1-rafael-1/pi-pico-alarmclock-rust/src/task/sound.rs

//! # Sound task
//!  This module contains the task that plays sound using the `DFPlayer` Mini module.
//!
//! The task is responsible for initializing the `DFPlayer` Mini module, powering it on, playing a sound, and powering it off.
use core::sync::atomic::{AtomicBool, Ordering};

use defmt::{Debug2Format, info};
use dfplayer_async::{DfPlayer, Equalizer, PlayBackSource, TimeSource};
use embassy_futures::select::{Either, select};
use embassy_rp::{
    gpio::{Input, Output},
    uart::BufferedUart,
};
use embassy_sync::{blocking_mutex::raw::CriticalSectionRawMutex, mutex::Mutex, signal::Signal};
use embassy_time::{Delay, Duration, Instant, Timer};

use crate::event::{Event, send_event};

/// Signal for starting the sound
static SOUND_START_SIGNAL: Signal<CriticalSectionRawMutex, ()> = Signal::new();

/// Signal for stopping the sound
static SOUND_STOP_SIGNAL: Signal<CriticalSectionRawMutex, ()> = Signal::new();

/// Tracks whether the `DFPlayer` is currently powered on
static DFPLAYER_POWERED: AtomicBool = AtomicBool::new(false);

/// Current volume level (protected by mutex)
static SOUND_VOLUME: Mutex<CriticalSectionRawMutex, u8> = Mutex::new(13);

/// Updates the current volume level
pub fn signal_sound_volume_update(volume: u8) {
    // We need to update the volume in the mutex
    // This will be picked up next time sound plays
    // Use try_lock to avoid blocking
    if let Ok(mut vol) = SOUND_VOLUME.try_lock() {
        *vol = volume;
    } else {
        info!("Volume update skipped: mutex locked");
    }
}

/// Gets the current volume level
async fn get_current_volume() -> u8 {
    let vol = SOUND_VOLUME.lock().await;
    *vol
}

/// Signals the sound task to start playing
pub fn signal_sound_start() {
    SOUND_START_SIGNAL.signal(());
}

/// Signals the sound task to stop playing
/// Only signals if the `DFPlayer` is currently powered to avoid pending signals
pub fn signal_sound_stop() {
    // Only signal stop if DFPlayer is actually powered and potentially playing
    if DFPLAYER_POWERED.load(Ordering::Relaxed) {
        SOUND_STOP_SIGNAL.signal(());
    } else {
        info!("Skipping sound stop signal - DFPlayer not powered");
    }
}

/// Waits for the next sound start signal
async fn wait_for_sound_start() {
    SOUND_START_SIGNAL.wait().await;
}

/// Waits for the next sound stop signal
async fn wait_for_sound_stop() {
    SOUND_STOP_SIGNAL.wait().await;
}

// Time source implementation for DFPlayer
/// Time source implementation for the `DFPlayer` using Embassy's `Instant`.
struct MyTimeSource;

impl TimeSource for MyTimeSource {
    type Instant = Instant;

    fn now(&self) -> Self::Instant {
        Instant::now()
    }

    fn is_elapsed(&self, since: Self::Instant, timeout_ms: u64) -> bool {
        Instant::now().duration_since(since) >= Duration::from_millis(timeout_ms)
    }
}

/// Waits for the busy pin to go high (indicating playback finished)
/// The busy pin is LOW during playback and HIGH when idle/finished
async fn wait_for_music_end(busy_pin: &mut Input<'static>) {
    // Wait for the pin to go high (song finished)
    // We add a small initial delay to ensure the pin has stabilized after starting playback
    Timer::after(Duration::from_millis(100)).await;
    busy_pin.wait_for_high().await;
}

/// Powers on the `DFPlayer` module and waits for it to stabilize
async fn power_on_dfplayer(pwr: &mut Output<'static>) {
    info!("Powering on the dfplayer");
    pwr.set_high();
    DFPLAYER_POWERED.store(true, Ordering::Relaxed);
    Timer::after(Duration::from_millis(500)).await;
    info!("Powered on the dfplayer");
}

/// Powers off the `DFPlayer` module
fn power_off_dfplayer(pwr: &mut Output<'static>) {
    info!("Powering off the dfplayer");
    pwr.set_low();
    DFPLAYER_POWERED.store(false, Ordering::Relaxed);
}

/// Handles the sound playback after `DFPlayer` initialization
async fn handle_playback(dfp: &mut DfPlayer<'_, BufferedUart, MyTimeSource, Delay>, busy_pin: &mut Input<'static>) {
    info!("Playing sound");

    // Step 1: Configure volume
    let volume = get_current_volume().await;
    info!("Setting volume to {}", volume);
    let _ = dfp.set_volume(volume).await;
    Timer::after(Duration::from_millis(100)).await;

    // Step 2: Set equalizer
    let _ = dfp.set_equalizer(Equalizer::Classic).await;
    Timer::after(Duration::from_millis(100)).await;

    // Step 3: Set playback source
    let _ = dfp.set_playback_source(PlayBackSource::SDCard).await;
    Timer::after(Duration::from_millis(100)).await;

    // Step 4: Start playback
    let _ = dfp.play(1).await;
    Timer::after(Duration::from_millis(200)).await;

    // Step 5: Wait for playback to complete
    wait_for_playback_end(busy_pin).await;
}

/// Waits for playback to end either by user action or song completion
async fn wait_for_playback_end(busy_pin: &mut Input<'static>) {
    let result = select(wait_for_sound_stop(), wait_for_music_end(busy_pin)).await;

    match result {
        Either::First(()) => {
            info!("Sound stopped by user");
        }
        Either::Second(()) => {
            info!("Sound finished playing (busy pin high)");
            // Notify that the alarm should stop since the song ended
            send_event(Event::AlarmStop).await;
        }
    }
}

/// Initializes the `DFPlayer` and handles playback if successful
async fn initialize_and_play(uart: &mut BufferedUart, busy_pin: &mut Input<'static>) {
    // Initialize DFPlayer
    let feedback_enable = false;
    let timeout = Duration::from_secs(1);
    let reset_duration_override = Some(Duration::from_millis(1000));

    let time_source = MyTimeSource;
    let delay = Delay;

    let dfp_result = DfPlayer::new(
        uart,
        feedback_enable,
        timeout.as_millis(),
        time_source,
        delay,
        reset_duration_override.map(|d| d.as_millis()),
    )
    .await;

    // Handle the result
    match dfp_result {
        Ok(mut dfp) => {
            info!("DfPlayer initialized successfully");
            handle_playback(&mut dfp, busy_pin).await;
        }
        Err(ref e) => {
            info!("DfPlayer initialization failed with error {:?}", Debug2Format(&e));
        }
    }
}

#[embassy_executor::task]
pub async fn sound_handler(mut uart: BufferedUart, mut pwr: Output<'static>, mut busy_pin: Input<'static>) {
    info!("Sound task started");

    loop {
        // Wait for start signal
        wait_for_sound_start().await;

        // Power on DFPlayer
        power_on_dfplayer(&mut pwr).await;

        // Initialize and play sound
        initialize_and_play(&mut uart, &mut busy_pin).await;

        // Power off DFPlayer
        power_off_dfplayer(&mut pwr);
    }
}
