1-rafael-1/pi-pico-alarmclock-rust/src/task/mod.rs

//! Tasks that make up the application.
pub mod alarm_settings;
pub mod alarm_trigger;
pub mod button_leds;
pub mod buttons;
pub mod display;
pub mod light_effects;
pub mod orchestrate;
pub mod power;
pub mod rtc_manager;
pub mod sound;
pub mod time_updater;
pub mod watchdog;
